TomFahey/DTA-MSc-Project/docs/_images/ClassDAmp.png

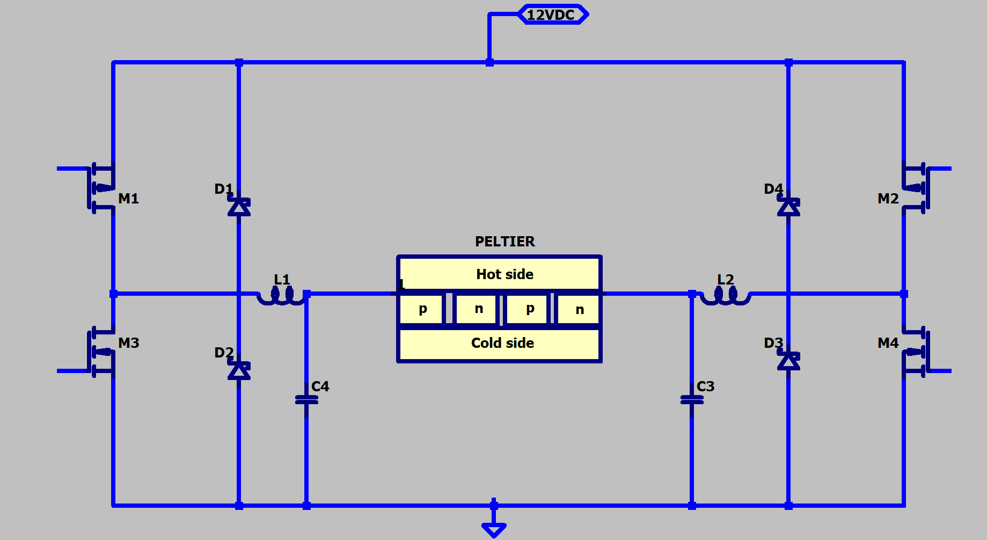
docs/_images/ClassDAmp.png
