TomFahey/DTA-MSc-Project/docs/_images/DifferentialThermocouple.png

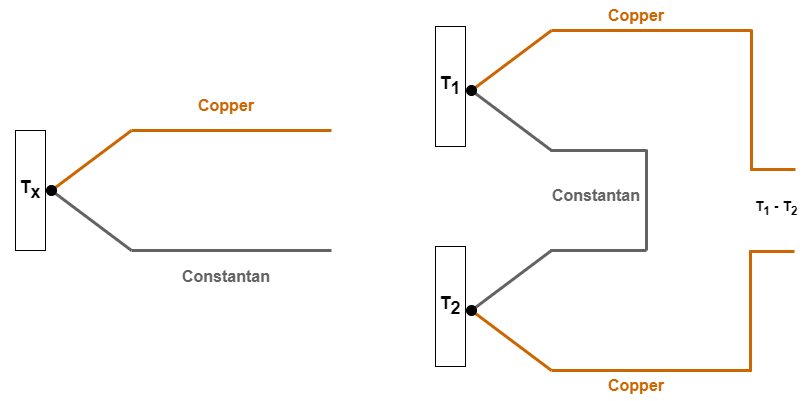
docs/_images/DifferentialThermocouple.png
