TomFahey/DTA-MSc-Project/docs/_images/settings.png

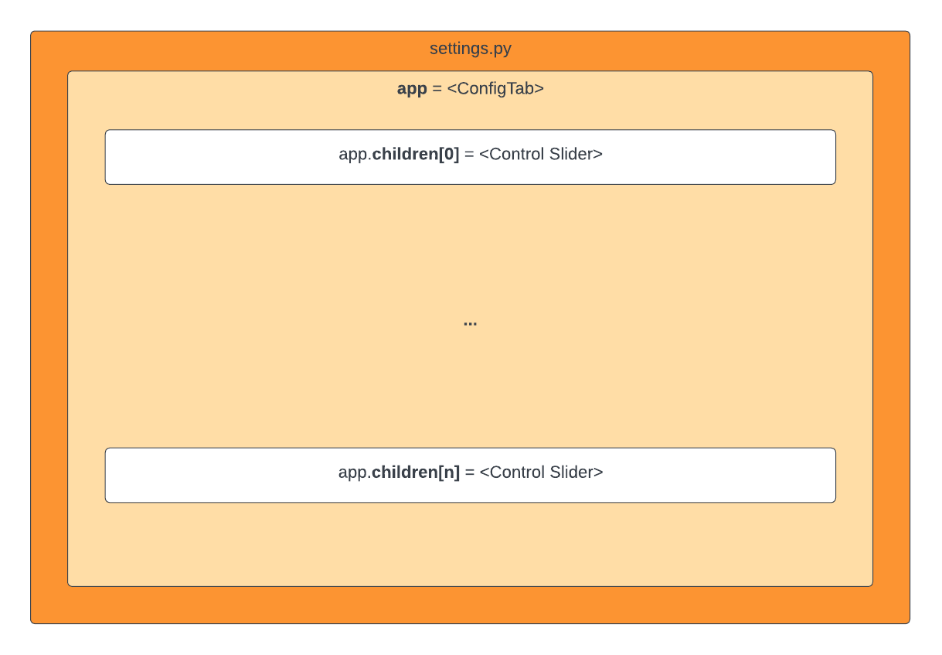
docs/_images/settings.png
