TomFahey/DTA-MSc-Project/docsrc/source/images/UserInterfaceMain.png

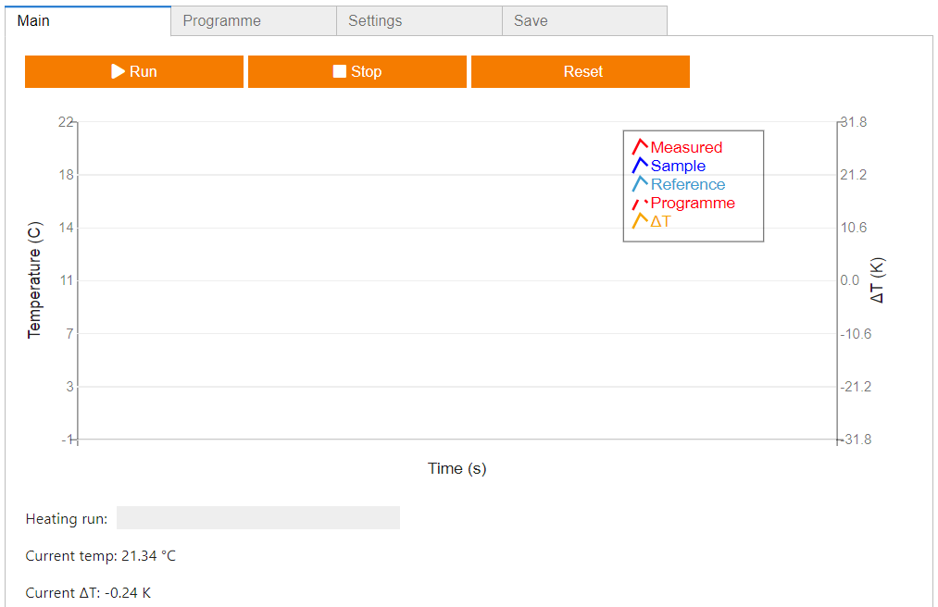
docsrc/source/images/UserInterfaceMain.png
