TomFahey/DTA-MSc-Project/docsrc/source/images/UserInterfaceProgrammeStages.png

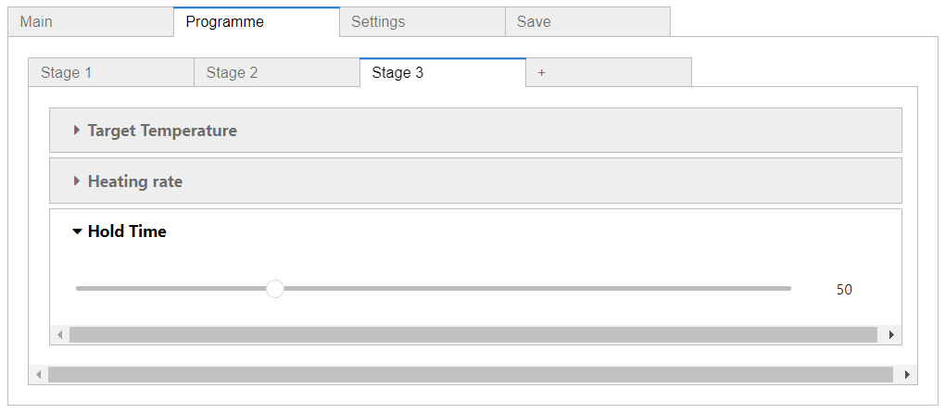
docsrc/source/images/UserInterfaceProgrammeStages.png
