TomFahey/DTA-MSc-Project/docsrc/build/html/_images/HAT-MDD10A.jpg

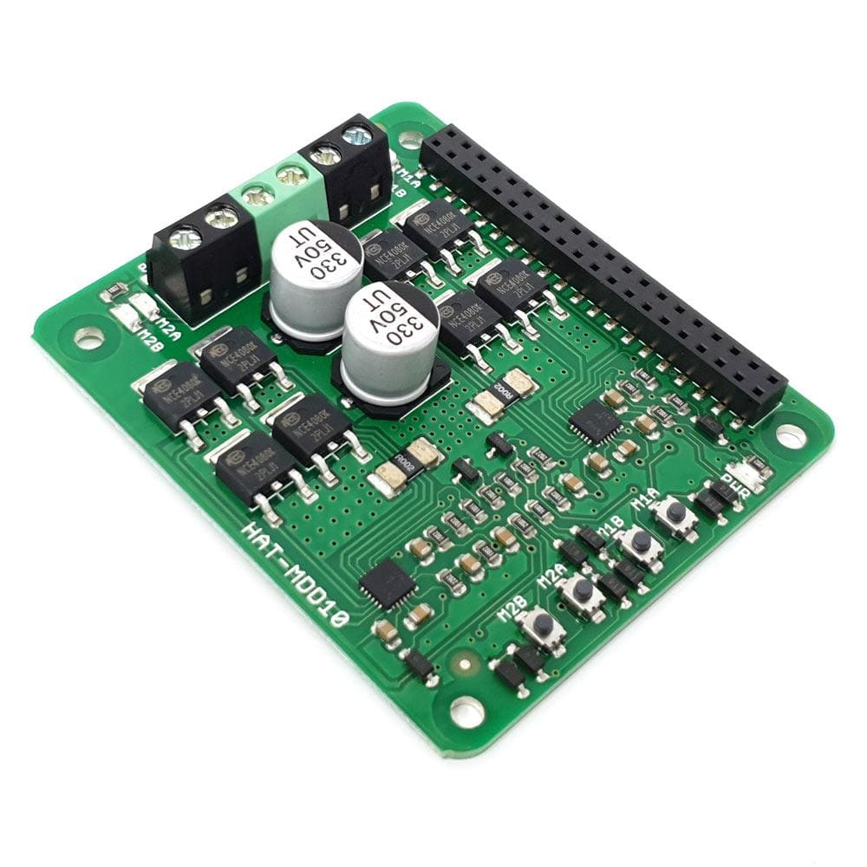
docsrc/build/html/_images/HAT-MDD10A.jpg
