TomFahey/DTA-MSc-Project/docsrc/build/html/_images/ThermoelectricModuleBoard.png

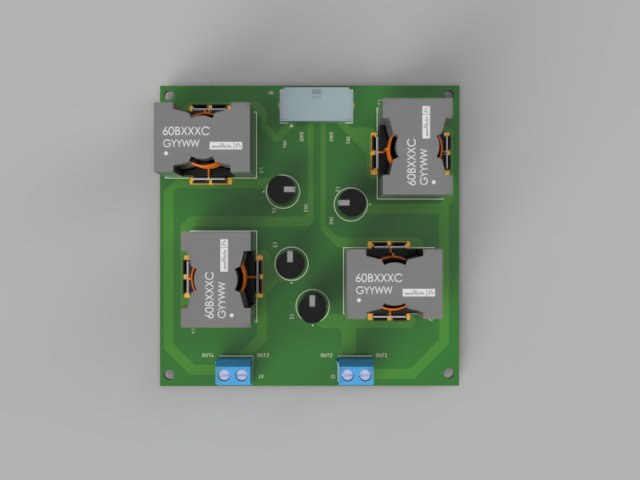
docsrc/build/html/_images/ThermoelectricModuleBoard.png
