TomFahey/DTA-MSc-Project/docs/_images/UserInterfaceJupyterDebugHighlight.png

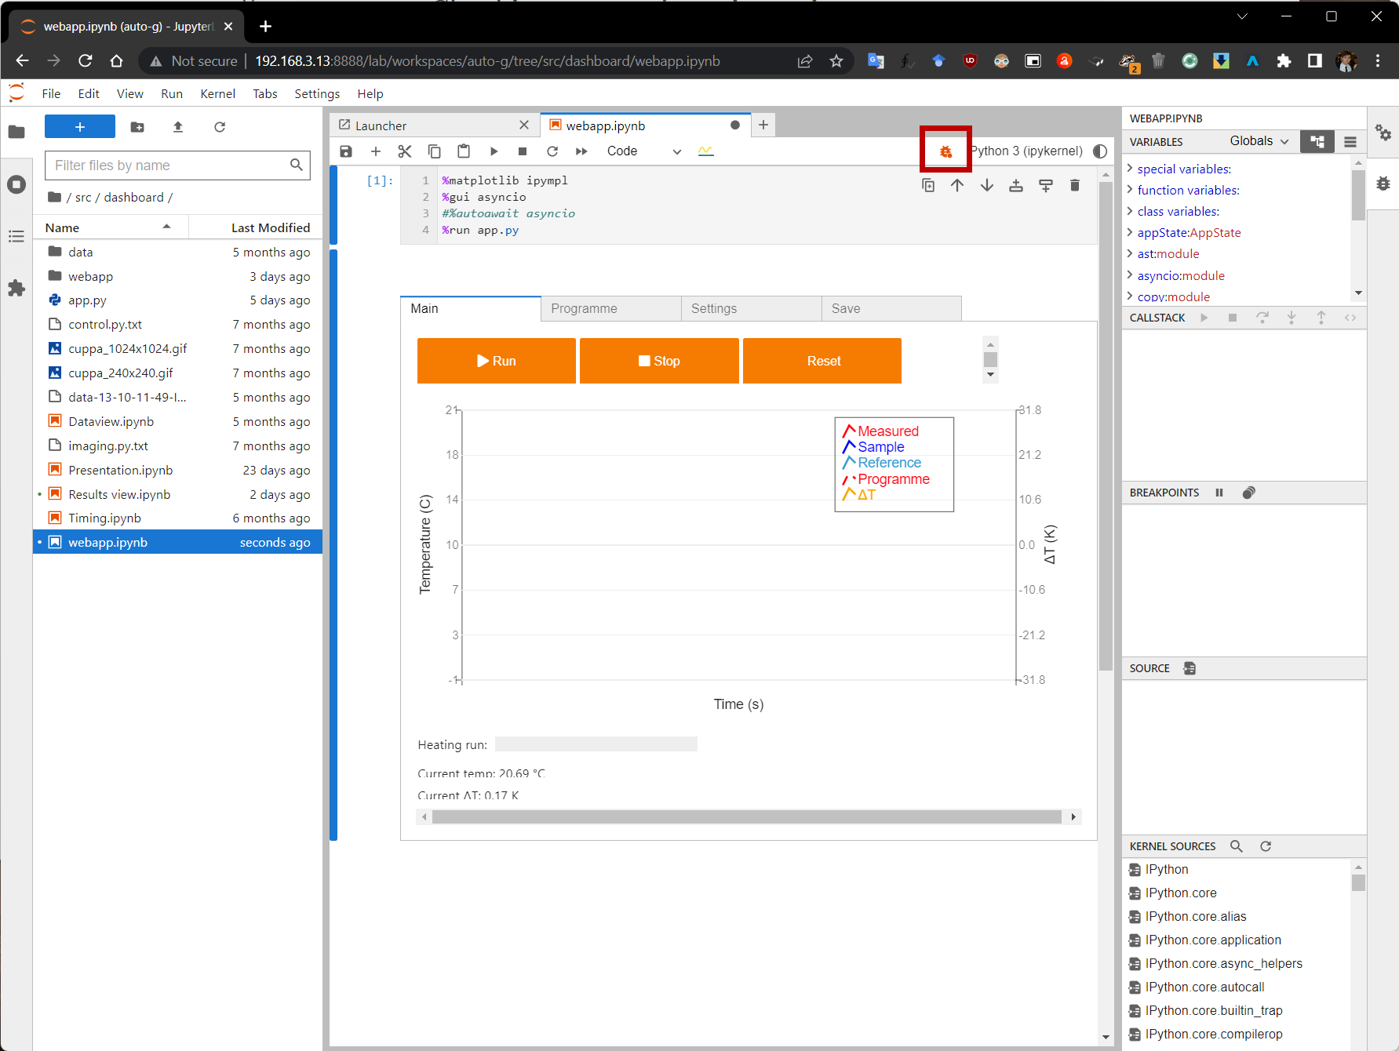
docs/_images/UserInterfaceJupyterDebugHighlight.png
